olell/LautIO/Software/LautIO/src/driver/wifi.cpp

/*
 *
 * This file is part of LautIO
 * 
 * Copyright 2021 - olel
 * LautIO is licensed under MIT License
 * See LICENSE file for more information
 * 
 */

#include "WiFi.h"

#include "sys_config.h"

// util
#include "util/log.h"
#include "util/config.h"
#include "driver/wifi.h"

// configuration values
const char* wifi_config_client_mode = "client";
const char* wifi_config_ap_mode = "ap";

// Fixed wifi parameter
IPAddress local_ip(10,0,0,1);
IPAddress gateway_ip(10,0,0,1);
IPAddress subnet_mask(255, 255, 255, 0);

bool wifi_connect_to_network() {
    /*
    This method tries to connect to the configured wifi network, it returns the success status as boolean
    */

    bool success = false;

    // Load client network parameter from config
    const char* ssid = Configuration::section("wifi")["ssid"];
    const char* pass = Configuration::section("wifi")["pass"];

    log_info("Starting to connect to WiFi network: %s", ssid);
    WiFi.mode(WIFI_STA);

    if (strcmp(pass, "") == 0) { // no wifi password
        WiFi.begin(ssid);
    }
    else {
        WiFi.begin(ssid, pass);
    }

    unsigned long connection_start_time = millis();
    unsigned long t_now = 0;

    bool first_try = true; // trying to connect two times; quick fix for issue https://github.com/olell/LautIO/issues/7

    wl_status_t wifi_status = WiFi.status();
    while (true) {

        if (wifi_status == WL_DISCONNECTED) {
            // Do nothing, waiting for connection
            t_now = millis();
            if (t_now - connection_start_time > 30000) { // 30 seconds timeout.. todo maybe this should be part of the config :O
                // Connection timeout reached
                log_warn("Couldn't connect.. connection timeout reached!");
                success = false;
                break;
            }
        }

        else if (wifi_status == WL_CONNECTED) {
            log_info("WiFi connection successfully established");
            log_info("My IP addr is: %s", WiFi.localIP().toString().c_str());

            success = true;
            break;
        }

        else if (wifi_status == WL_NO_SSID_AVAIL) {
            log_warn("SSID \"%s\" not found..", ssid);
            success = false;
            break;
        }

        else if (wifi_status == WL_CONNECT_FAILED) {
            log_warn("WiFi connection failed, maybe invalid credentials?");
            if (first_try) {
                log_info("Trying to connect a second time.");
                WiFi.begin(ssid, pass);
                delay(500);
            }
            else {
                success = false;
                break;
            }
            
        }

        delay(500);
        wifi_status = WiFi.status();

    }

    return success;

}

bool wifi_start_accesspoint() {
    /*
    This method starts an accesspoint with the configured credentials
    */

    bool success = false;

    // Load access point parameter from config
    const char* ssid = Configuration::section("wifi")["ap_ssid"];
    const char* pass = Configuration::section("wifi")["ap_pass"];

    log_info("Starting Access Point @ %s", ssid);

    WiFi.mode(WIFI_AP);
    WiFi.enableAP(true);
    WiFi.softAP(ssid, pass);

    log_debug("Started AP, waiting a bit");
    delay(2000);
    log_debug("AP will be ready soon!");

    WiFi.softAPConfig(local_ip, gateway_ip, subnet_mask);
    log_info("Access Point up and running!");

    success = true; // hmm
    return success;
}

void init_wifi() {

    // Load all base config parameters
    const char* mode = Configuration::section("wifi")["mode"];

    if (strcmp(mode, wifi_config_client_mode) == 0) {
        log_info("Initialising wifi driver in client mode");

        // Load client mode specific config parameter
        const bool fallback_ap = Configuration::section("wifi")["fallback_ap"];
        
        bool success = wifi_connect_to_network();

        if (!success && fallback_ap) {
            // start fallback access point
            log_warn("Failed to connect to network.. starting fallback Access Point");
            wifi_start_accesspoint();
        }

    }

    else if (strcmp(mode, wifi_config_ap_mode) == 0) {
        log_info("Initialising wifi driver in ap mode");
        wifi_start_accesspoint();
    }

}
