olell/LautIO/Software/LautIO/src/driver/battery.h

/*
 *
 * This file is part of LautIO
 * 
 * Copyright 2021 - olel
 * LautIO is licensed under MIT License
 * See LICENSE file for more information
 * 
 */

#pragma once

#include "Arduino.h"
#include "sys_config.h"

void init_battery() {
    //
    pinMode(VBAT_MEASURE, INPUT);
}

float get_battery_voltage() {
    // Get battery voltage in volts
    uint16_t adc_input = analogRead(VBAT_MEASURE);
    float vin;
    if (adc_input > 3000) {
        vin = 0.0005 * adc_input + 1.0874;
    }
    else {
        vin = 0.0008 * adc_input + 0.1372;
    }
    return vin * 16.0303;
}
